pavhofman/speaker-adapter/models/front_panels/front-panel-text.png

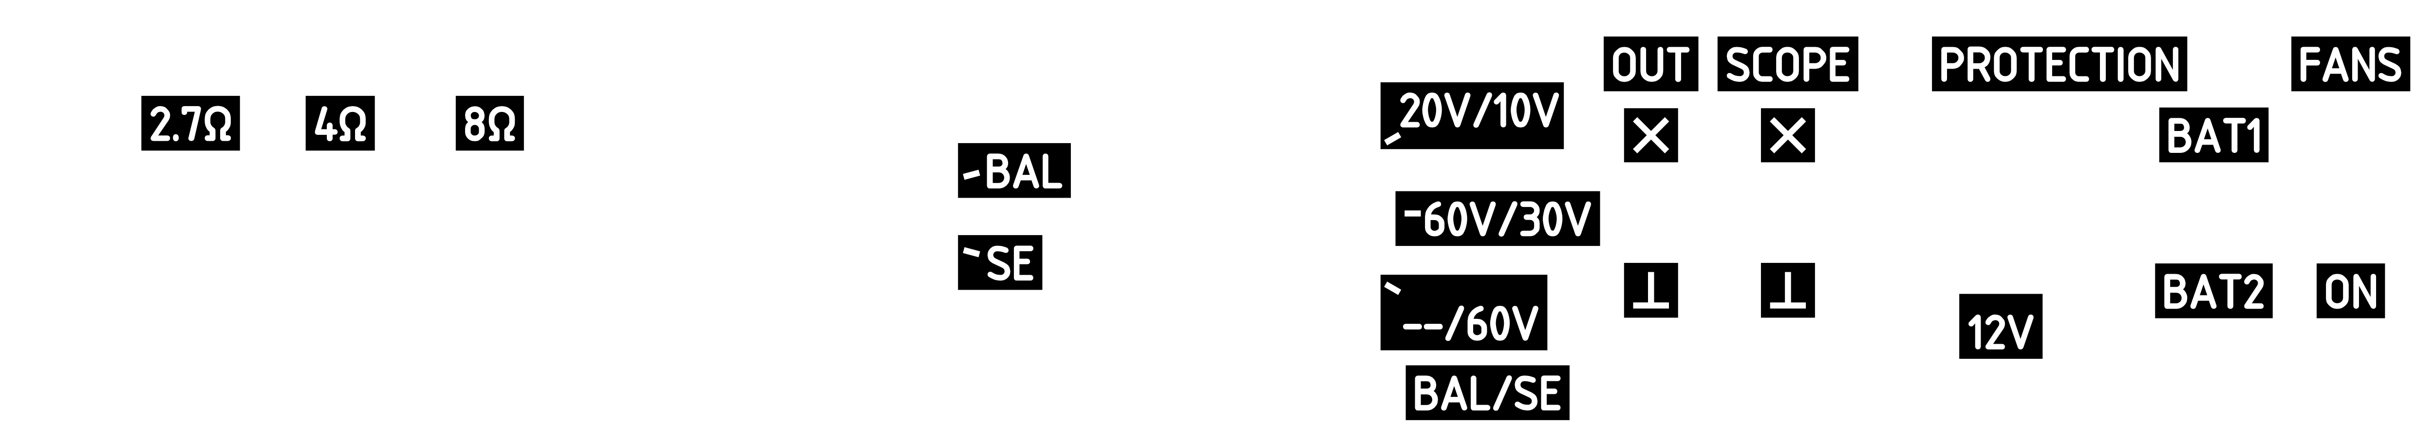
models/front_panels/front-panel-text.png
